leonhiem/codeswitch2/firmware/codeswitch2/samd11/astudio/utils.h

/*
 * Kamworks Codeswitch firmware
 *
 * Author: Leon Hiemstra <l.hiemstra@gmail.com>
 */

#ifndef _UTILS_H
#define _UTILS_H

#include <stdlib.h>
#include <stdint.h>
#include <string.h>

void delay_ms(unsigned long ms);
char is_digit(char c);
int decode_rcode(char *code_str, uint8_t *seq, uint32_t *id, uint16_t *days);

#endif // _UTILS_H
